paco7828/universal-remote/v5/uniremote/IR-codes.h

#pragma once

constexpr uint8_t MAX_IR_VARIANTS = 3;
constexpr uint8_t IR_CODE_LEN = 150;

struct IRCode {
  const char *codeName;
  uint8_t variantCount;
  const uint16_t codeArray[MAX_IR_VARIANTS][IR_CODE_LEN];
};

const IRCode EPSON_CODES[4] = {
  { "FREEZE", 2, { { 0x0000, 0x006D, 0x0000, 0x0022, 0x0153, 0x00AA, 0x0015, 0x0040, 0x0015, 0x003F, 0x0015, 0x0016, 0x0015, 0x0015, 0x0015, 0x0015, 0x0015, 0x0016, 0x0015, 0x0015, 0x0015, 0x003F, 0x0016, 0x003F, 0x0015, 0x0016, 0x0015, 0x0040, 0x0015, 0x0015, 0x0015, 0x0040, 0x0015, 0x0015, 0x0015, 0x0040, 0x0015, 0x0015, 0x0015, 0x0015, 0x0015, 0x0040, 0x0015, 0x0015, 0x0015, 0x0016, 0x0016, 0x003F, 0x0015, 0x0015, 0x0015, 0x0016, 0x0015, 0x003F, 0x0015, 0x0040, 0x0015, 0x0015, 0x0015, 0x0040, 0x0015, 0x003F, 0x0015, 0x0016, 0x0016, 0x003F, 0x0015, 0x0040, 0x0015, 0x0015, 0x0015, 0x05BF }, { 0x0000, 0x006C, 0x0022, 0x0000, 0x015B, 0x00AD, 0x0016, 0x0041, 0x0016, 0x0041, 0x0016, 0x0016, 0x0016, 0x0016, 0x0016, 0x0016, 0x0016, 0x0016, 0x0016, 0x0016, 0x0016, 0x0041, 0x0016, 0x0041, 0x0016, 0x0016, 0x0016, 0x0041, 0x0016, 0x0016, 0x0016, 0x0041, 0x0016, 0x0016, 0x0016, 0x0041, 0x0016, 0x0016, 0x0016, 0x0041, 0x0016, 0x0041, 0x0016, 0x0041, 0x0016, 0x0016, 0x0016, 0x0016, 0x0016, 0x0016, 0x0016, 0x0041, 0x0016, 0x0016, 0x0016, 0x0016, 0x0016, 0x0016, 0x0016, 0x0016, 0x0016, 0x0041, 0x0016, 0x0041, 0x0016, 0x0041, 0x0016, 0x0016, 0x0016, 0x0041, 0x0016, 0x0622 } } },
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
};

const uint8_t MIDEA_CODES_LENGTH = sizeof(MIDEA_CODES) / sizeof(MIDEA_CODES[0]);
